gbevin/tactile-patch-sheets/Components/DFAM Tactile Patch Sheets Components/DFAM Build overlay extruded right.stp

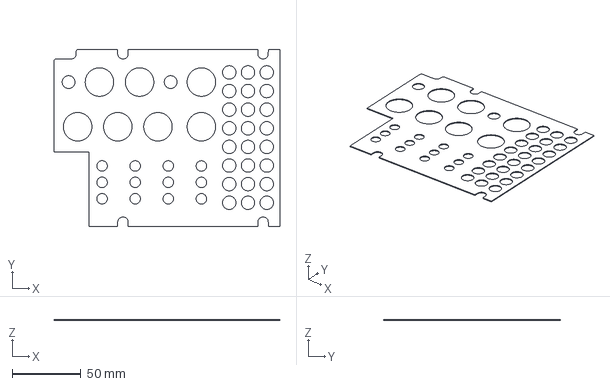
[picture p5: CAD file, 2023-08-12]
Components/DFAM Tactile Patch Sheets Components/DFAM Build overlay extruded right.stp
163.9 x 128.5 x 0.65 mm
