gbevin/tactile-patch-sheets/Components/DFAM Tactile Patch Sheets Components/DFAM Build overlay extruded left.stp

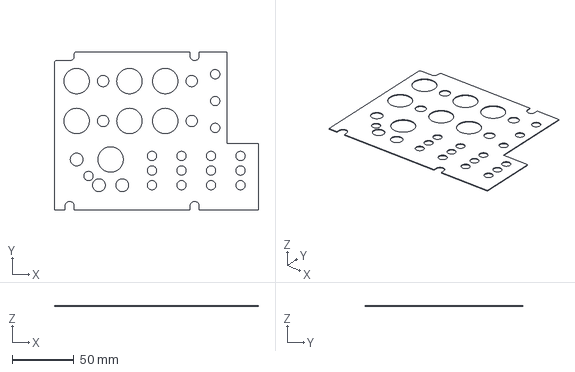
[picture p6: CAD file, 2023-08-12]
Components/DFAM Tactile Patch Sheets Components/DFAM Build overlay extruded left.stp
165.8 x 128.5 x 0.65 mm
