gbevin/tactile-patch-sheets/Components/MAVIS Tactile Patch Sheets Components/MAVIS Build overlay identity markers.stp

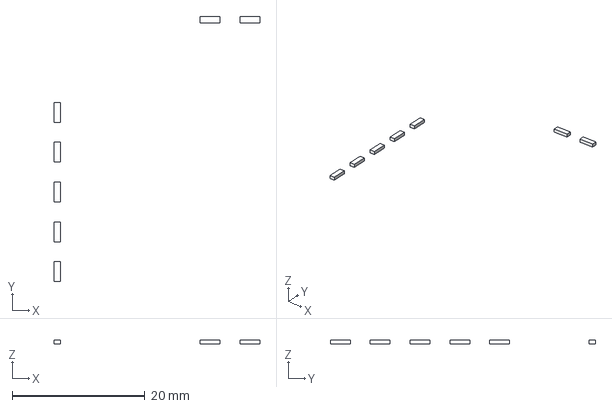
[picture p7: CAD file, 2023-08-12]
Components/MAVIS Tactile Patch Sheets Components/MAVIS Build overlay identity markers.stp
31.0 x 39.9 x 0.65 mm
Build marker identity x 7
