gbevin/tactile-patch-sheets/Components/MAVIS Tactile Patch Sheets Components/MAVIS Build overlay extruded.stp

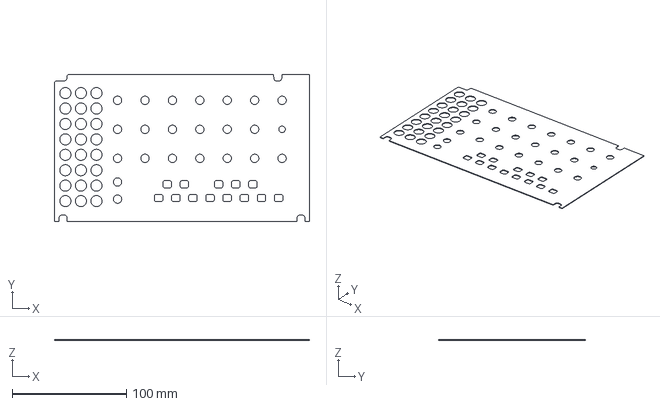
[picture p8: CAD file, 2023-08-12]
Components/MAVIS Tactile Patch Sheets Components/MAVIS Build overlay extruded.stp
223.2 x 128.5 x 0.65 mm
