gbevin/tactile-patch-sheets/Components/DFAM Tactile Patch Sheets Components/DFAM Build overlay identity markers.stp

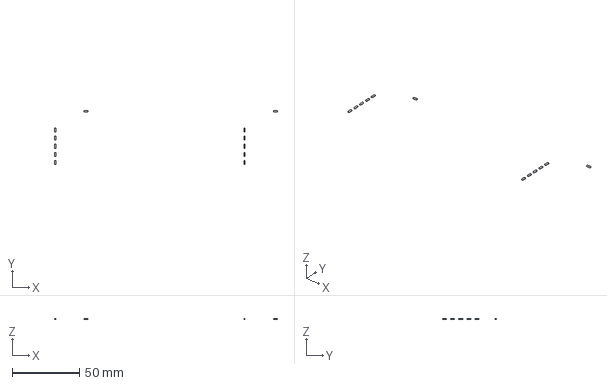
[picture p9: CAD file, 2023-08-12]
Components/DFAM Tactile Patch Sheets Components/DFAM Build overlay identity markers.stp
165.4 x 39.9 x 0.65 mm
Build marker identity x 12
